impatrq/asmb/Docs/Certificado Prototipos 2.jpg

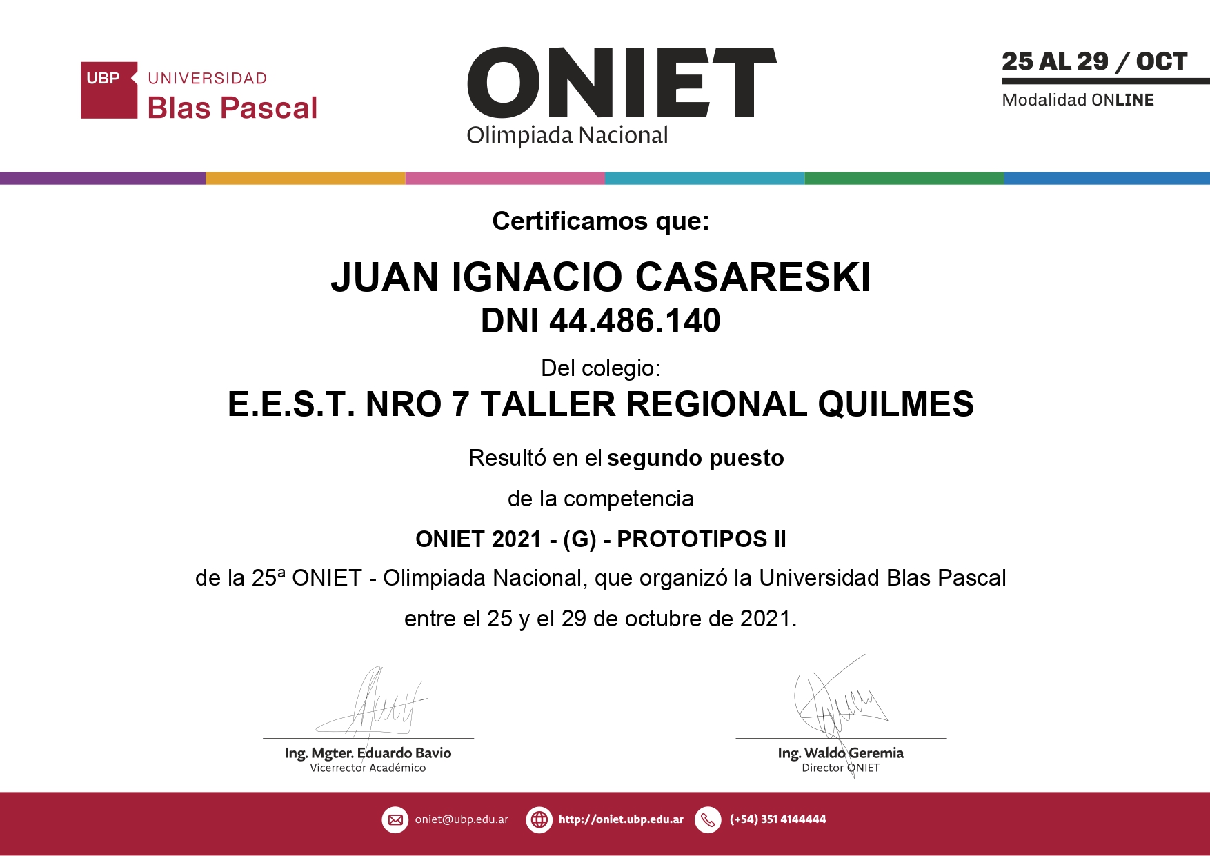
Docs/Certificado Prototipos 2.jpg
