impatrq/asmb/Docs/Imagenes/Adaptador de señal.png

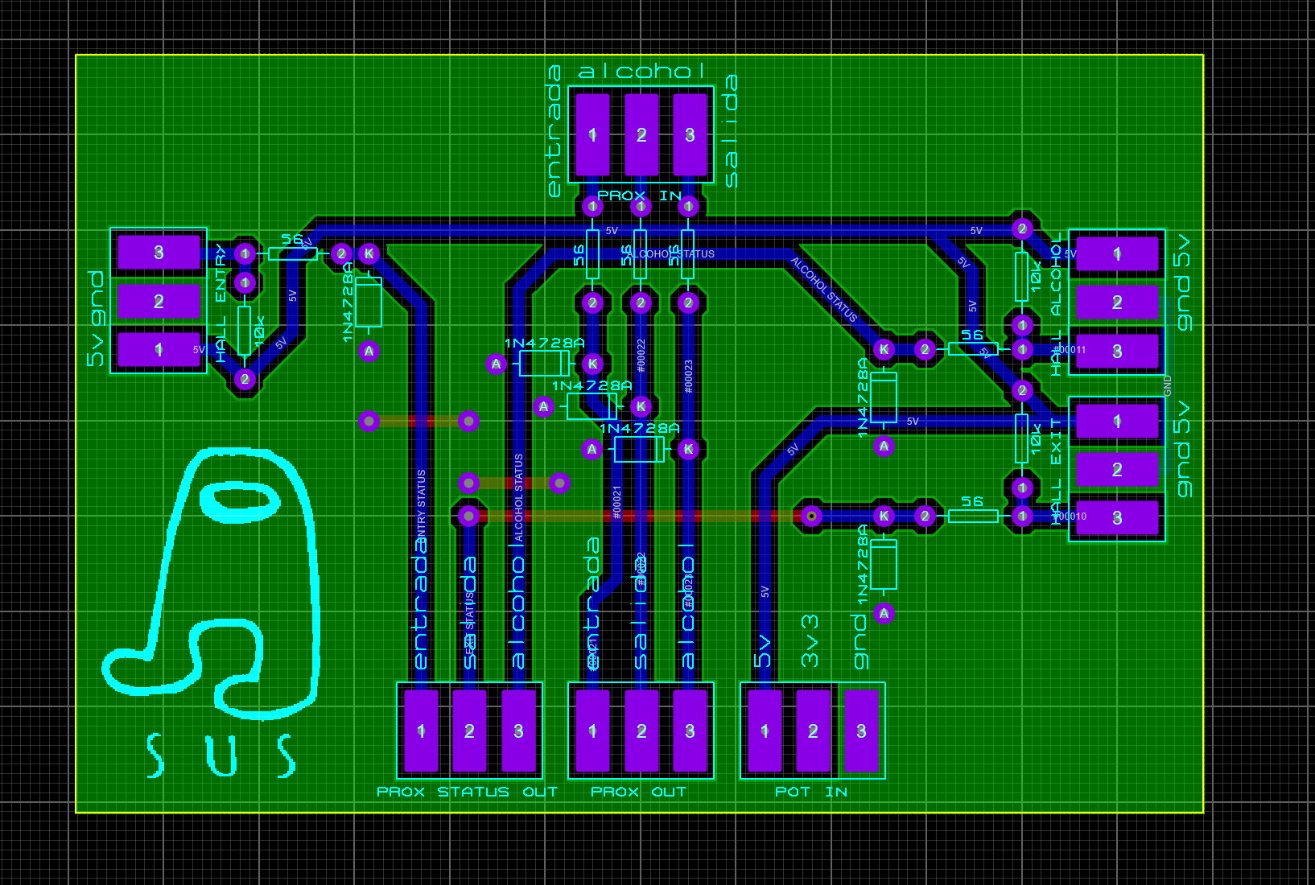
Docs/Imagenes/Adaptador de señal.png
