impatrq/asmb/Docs/Imagenes/Diagrama en Bloques.png

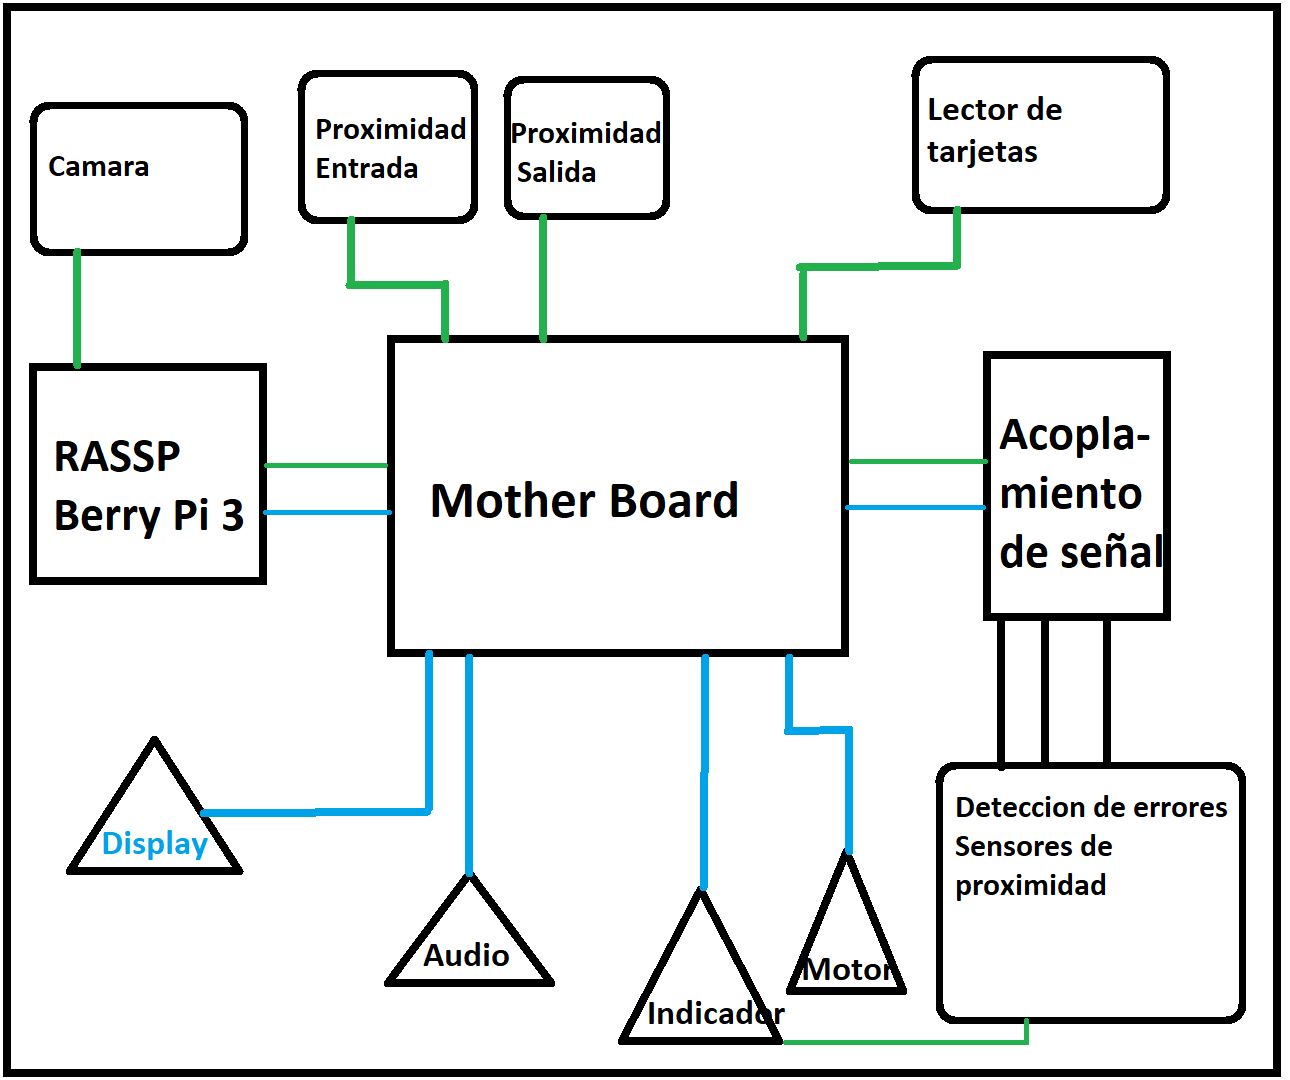
Docs/Imagenes/Diagrama en Bloques.png
