impatrq/asmb/Historias de Usuario/HU009 - Dispenser de alcohol/A1 - Croquis/Croquis.jpeg

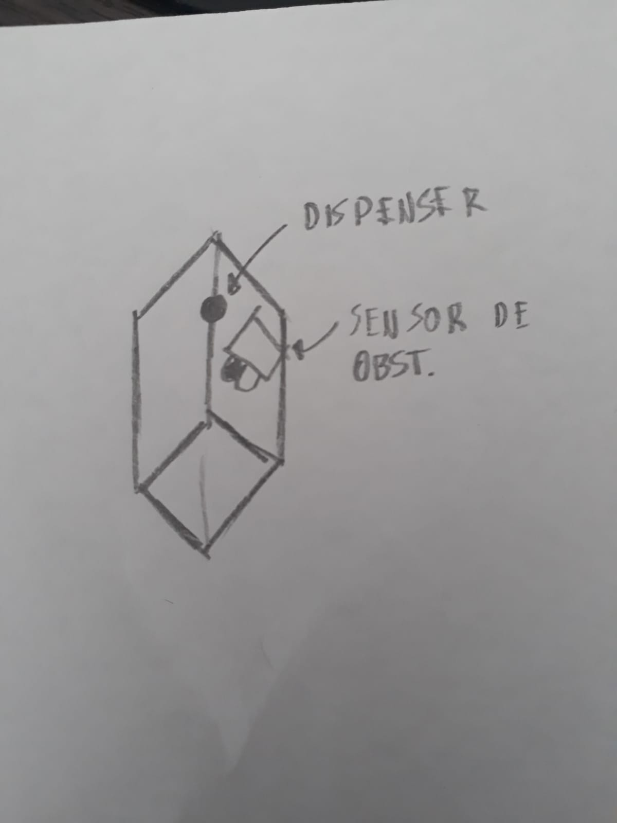
Historias de Usuario/HU009 - Dispenser de alcohol/A1 - Croquis/Croquis.jpeg
