impatrq/asmb/Historias de Usuario/HU009 - Dispenser de alcohol/A3 - Modelo 3d/Foto.png

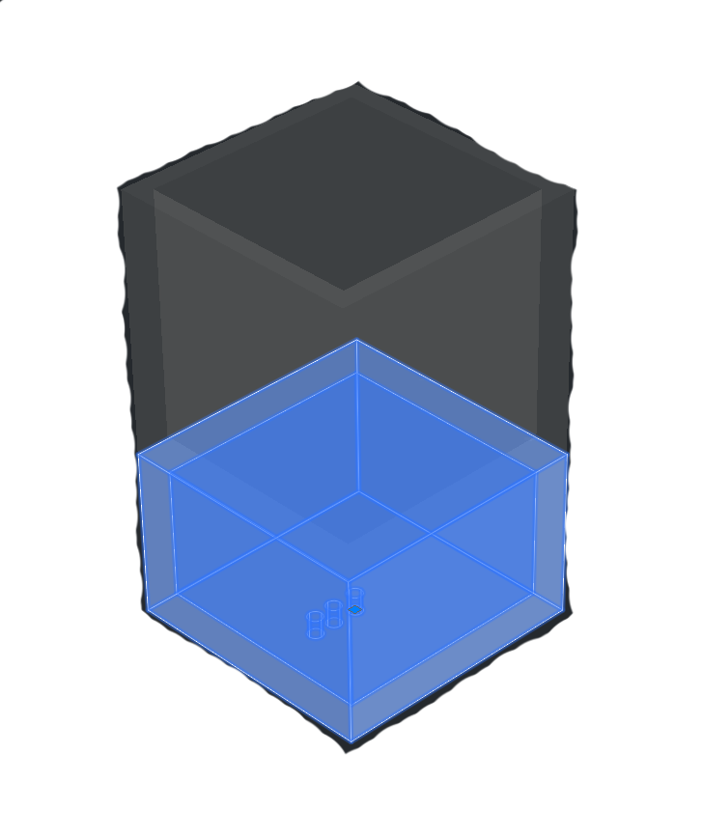
Historias de Usuario/HU009 - Dispenser de alcohol/A3 - Modelo 3d/Foto.png
