impatrq/asmb/Historias de Usuario/HU111 - Face recog/Resources/py_tutorials/py_ml/py_knn/py_knn_understanding/images/knn_theory.png

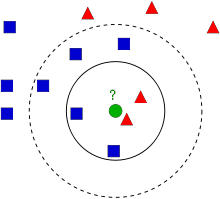
Historias de Usuario/HU111 - Face recog/Resources/py_tutorials/py_ml/py_knn/py_knn_understanding/images/knn_theory.png
