impatrq/asmb/Historias de Usuario/HU016 - Check In Empleados/A1 - Croquis/Croquis.jpeg

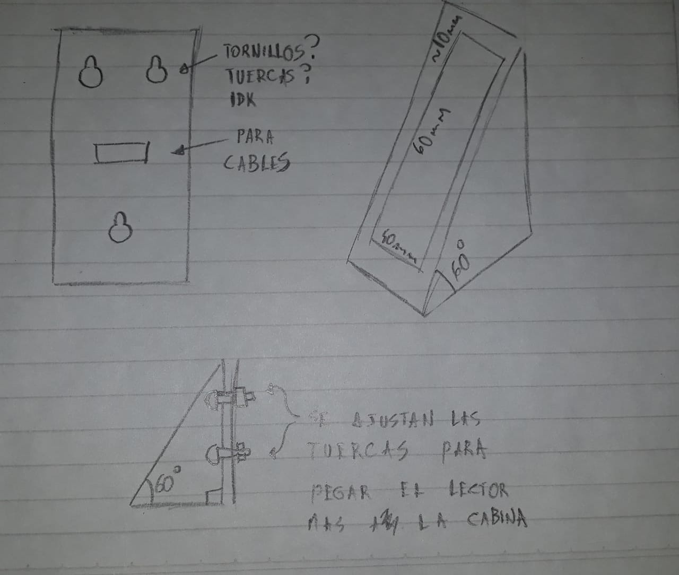
Historias de Usuario/HU016 - Check In Empleados/A1 - Croquis/Croquis.jpeg
