impatrq/asmb/Historias de Usuario/HU016 - Check In Empleados/A2 - Lugar en el croquis/Lugar en el croquis.png

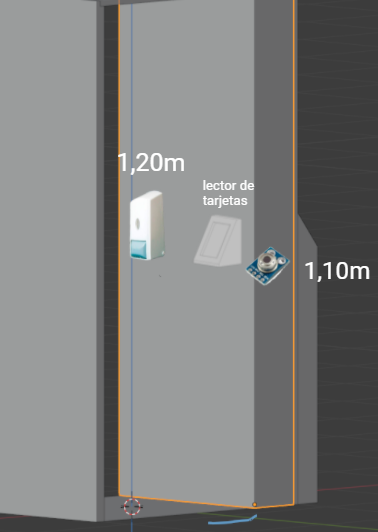
Historias de Usuario/HU016 - Check In Empleados/A2 - Lugar en el croquis/Lugar en el croquis.png
