impatrq/asmb/Historias de Usuario/HU016 - Check In Empleados/A3 - Modelo 3d/Foto del lector de tarjetas.png

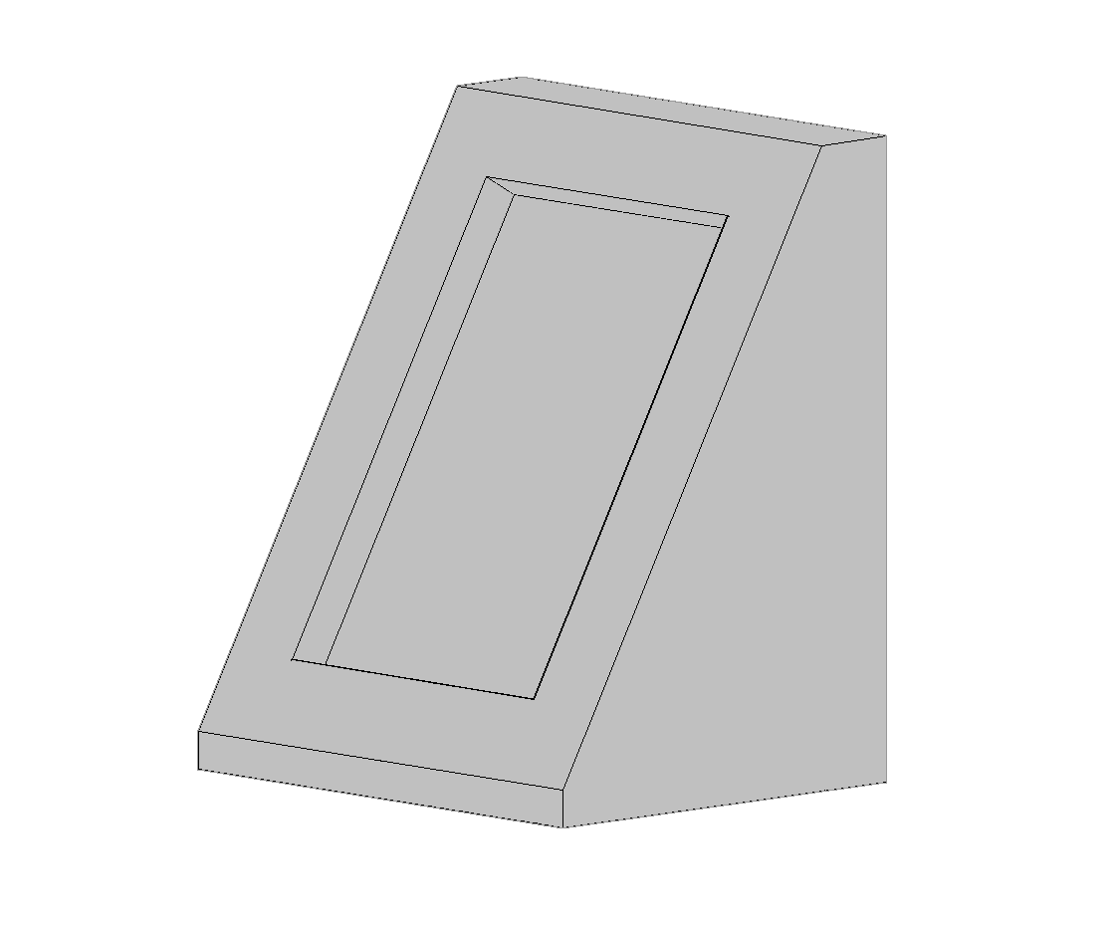
Historias de Usuario/HU016 - Check In Empleados/A3 - Modelo 3d/Foto del lector de tarjetas.png
