impatrq/asmb/Recursos/Circuitos/Dispenser de alcohol/Circuito dispenser.jpeg

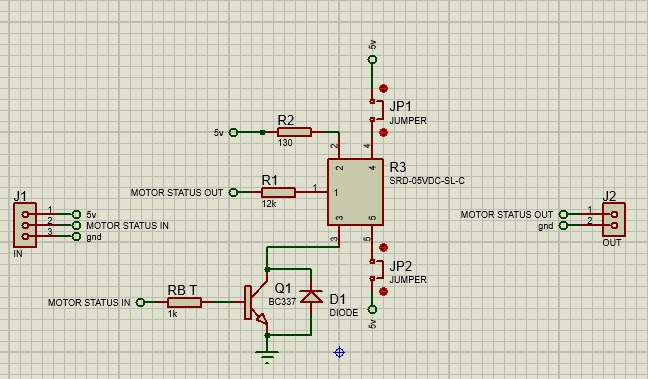
Recursos/Circuitos/Dispenser de alcohol/Circuito dispenser.jpeg
