impatrq/asmb/Recursos/Circuitos/Lector de tarjetas/Foto cirucito lector.jpeg

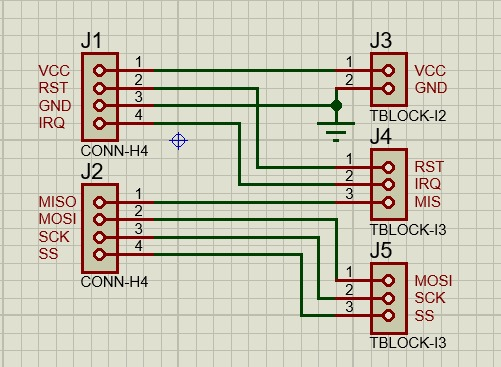
Recursos/Circuitos/Lector de tarjetas/Foto cirucito lector.jpeg
