impatrq/asmb/Recursos/Circuitos/Mother/Foto ciruito mother.jpeg

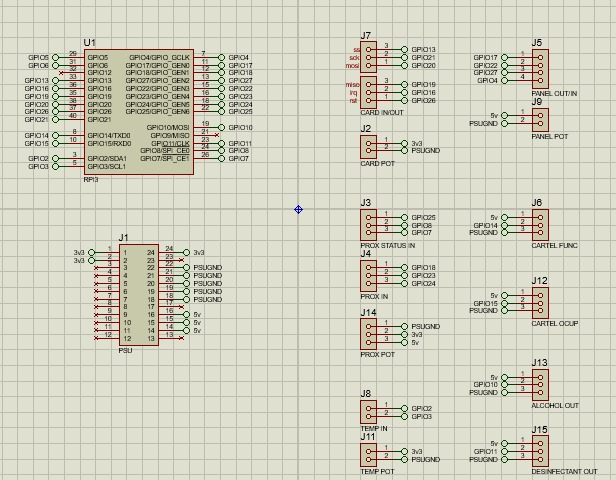
Recursos/Circuitos/Mother/Foto ciruito mother.jpeg
