impatrq/asmb/Recursos/Circuitos/Panel de estado/Foto circuito panel.jpeg

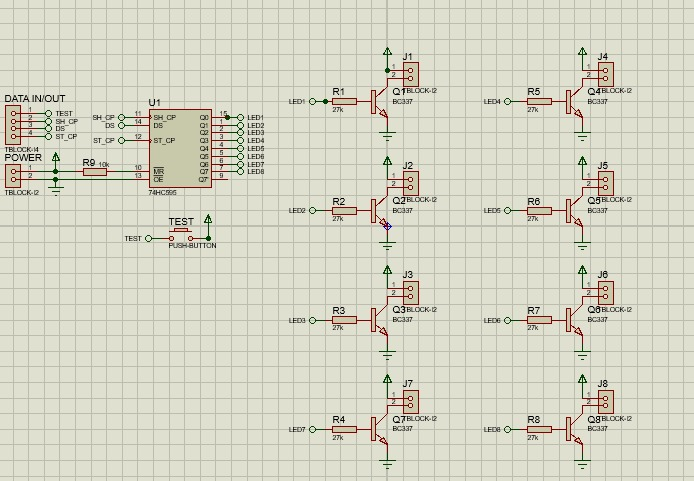
Recursos/Circuitos/Panel de estado/Foto circuito panel.jpeg
