impatrq/asmb/Recursos/Circuitos/Proximity sensors/Foto circuito Level.jpeg

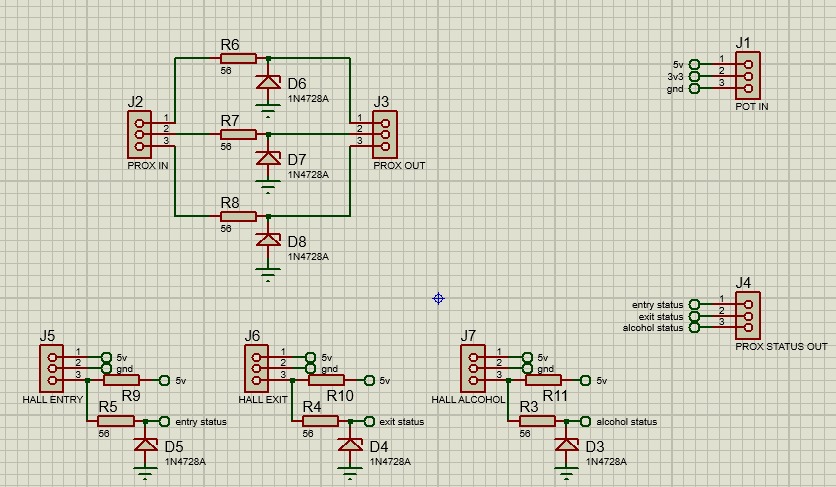
Recursos/Circuitos/Proximity sensors/Foto circuito Level.jpeg
