impatrq/asmb/Recursos/Modelos/Cabina general/Modelo Cabina General.jpeg

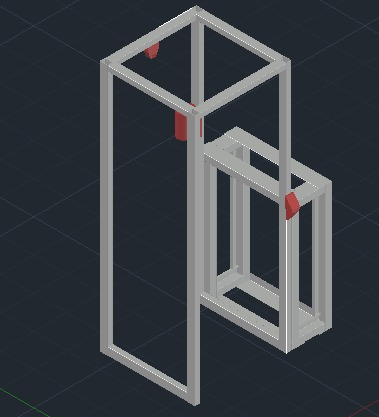
Recursos/Modelos/Cabina general/Modelo Cabina General.jpeg
