impatrq/asmb/Recursos/Modelos/Cartel ocupado/Cartel Ocupado.jpeg

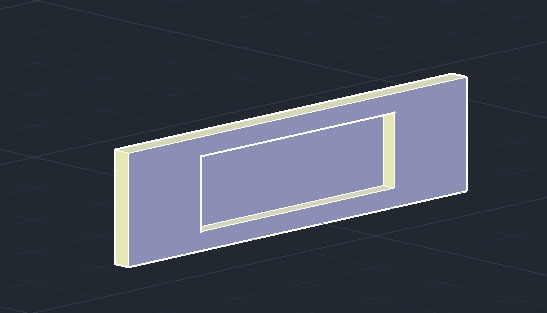
Recursos/Modelos/Cartel ocupado/Cartel Ocupado.jpeg
