impatrq/asmb/Recursos/Modelos/Dispenser de alcohol en gel/Dispenser.jpeg

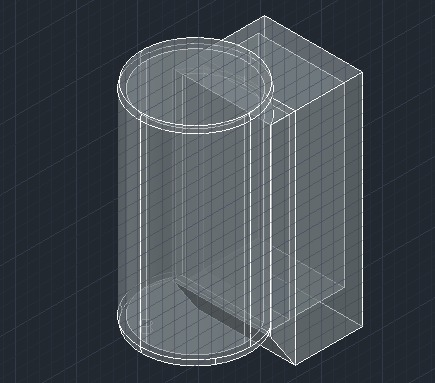
Recursos/Modelos/Dispenser de alcohol en gel/Dispenser.jpeg
