impatrq/asmb/Recursos/Modelos/Lector de tarjetas/Lector.jpeg

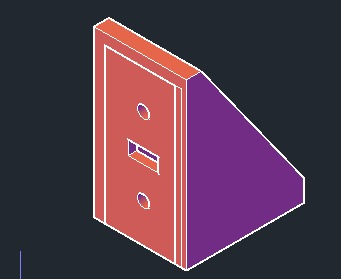
Recursos/Modelos/Lector de tarjetas/Lector.jpeg
