impatrq/asmb/Recursos/Modelos/Sensor de temperatura/Sensor de temp..jpeg

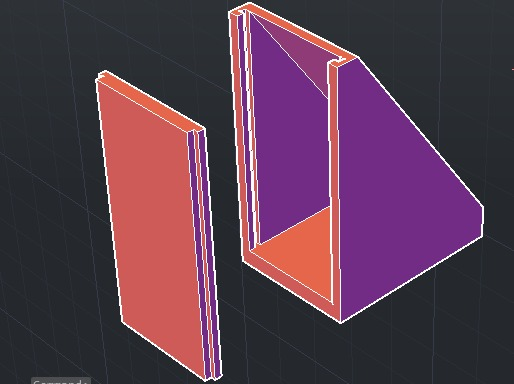
Recursos/Modelos/Sensor de temperatura/Sensor de temp..jpeg
