impatrq/asmb/Recursos/Video Presentación/Fotos/26c4ca4a28fdd9ee4a0b5ad8b2b49a2f3947dffb_full.jpg

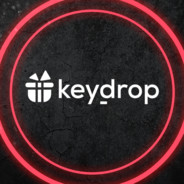
Recursos/Video Presentación/Fotos/26c4ca4a28fdd9ee4a0b5ad8b2b49a2f3947dffb_full.jpg
