impatrq/asmb/Recursos/Video Presentación/Fotos/CASI XD.jpg

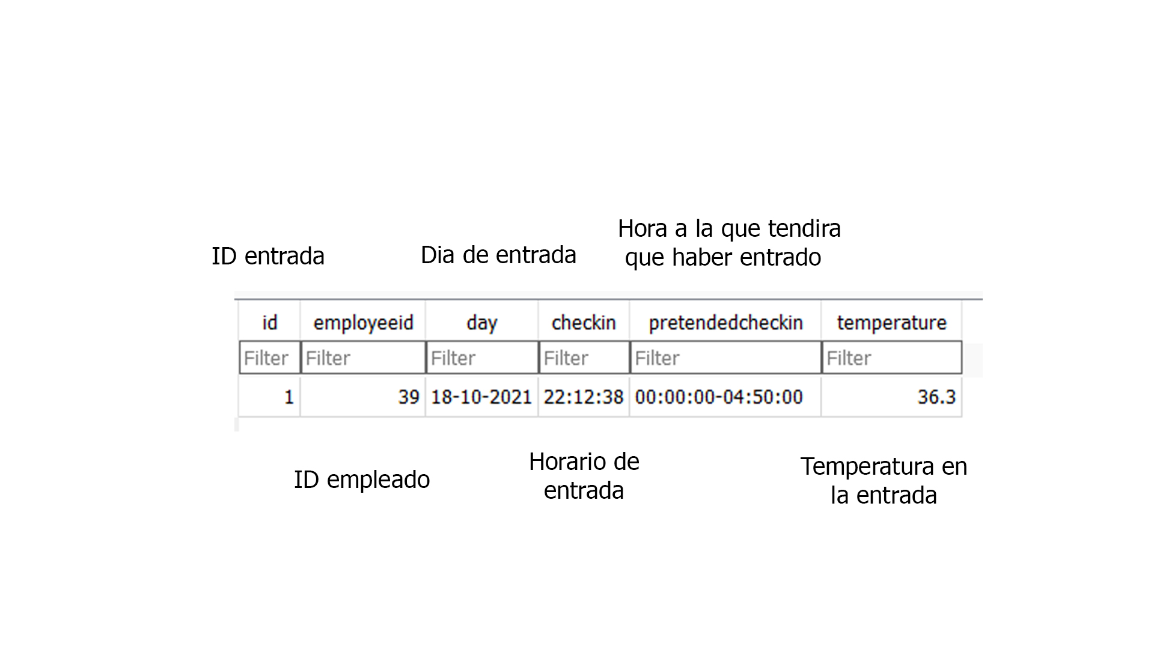
Recursos/Video Presentación/Fotos/CASI XD.jpg
