impatrq/asmb/Recursos/Video Presentación/Fotos/entrada_aeropuerto_2.jpg

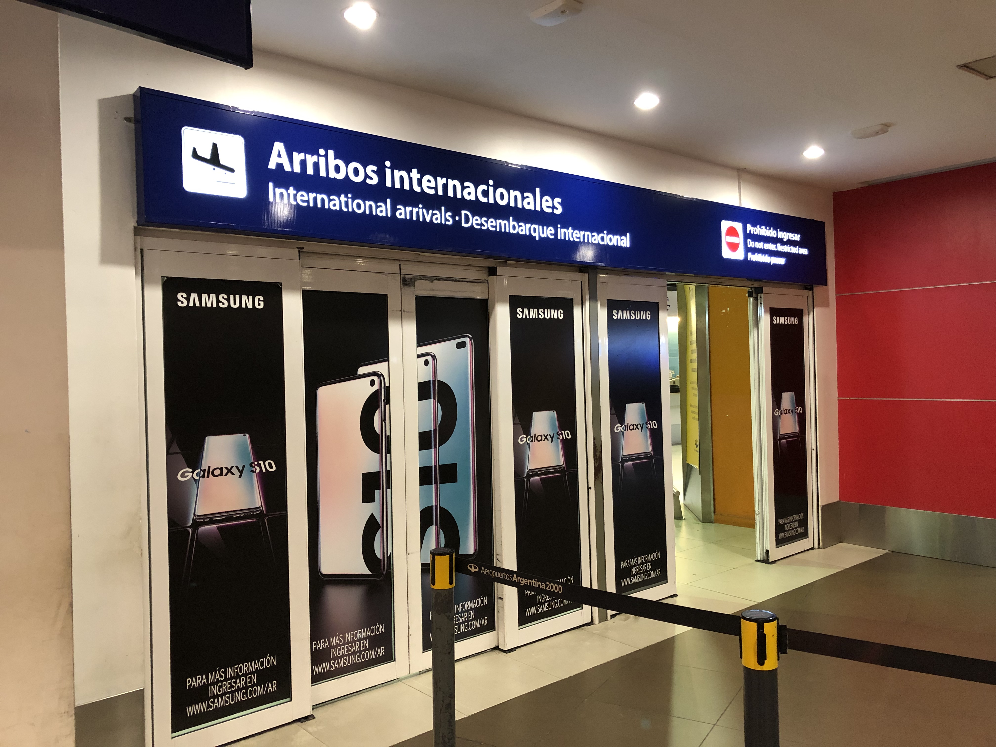
Recursos/Video Presentación/Fotos/entrada_aeropuerto_2.jpg
