impatrq/asmb/Recursos/Video Presentación/Fotos/entrada_comercio_4.jpg

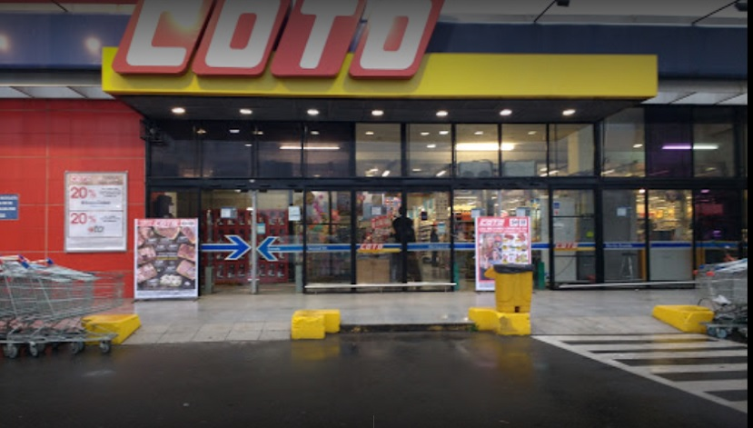
Recursos/Video Presentación/Fotos/entrada_comercio_4.jpg
