impatrq/asmb/Recursos/Video Presentación/Fotos/entrada_escuela_3.jpg

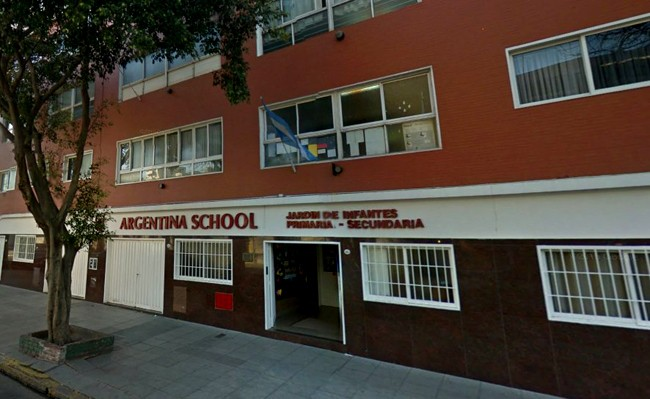
Recursos/Video Presentación/Fotos/entrada_escuela_3.jpg
