impatrq/asmb/Recursos/Video Presentación/Fotos/hospital_frente_1 (1).jpg

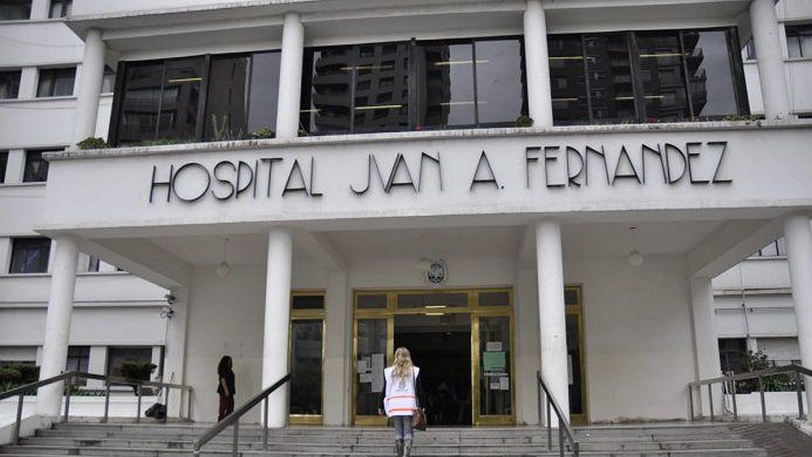
Recursos/Video Presentación/Fotos/hospital_frente_1 (1).jpg
