impatrq/asmb/Recursos/Video Presentación/Fotos/Muestras de proyectos.jpg

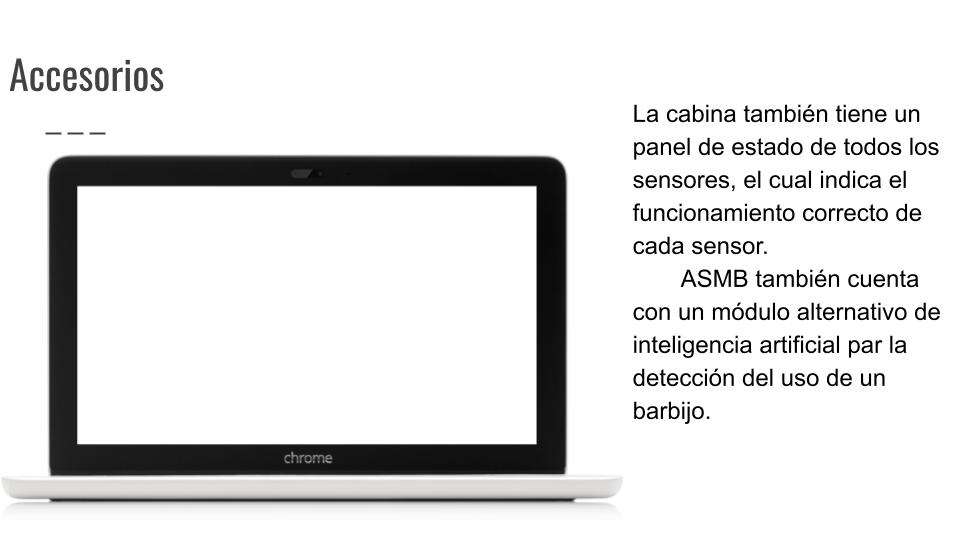
Recursos/Video Presentación/Fotos/Muestras de proyectos.jpg
