impatrq/asmb/Recursos/Video Presentación/Fotos/Muestras_de_proyectos.jpg

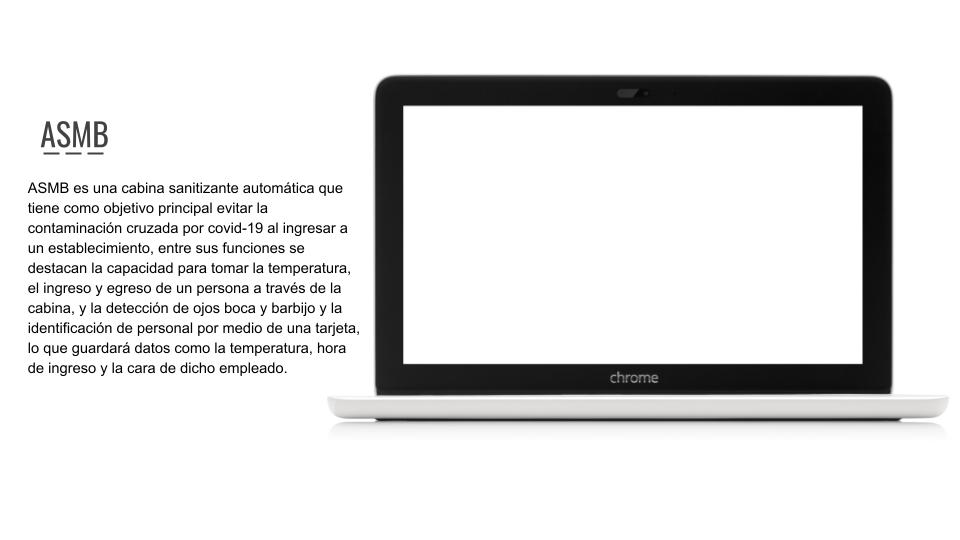
Recursos/Video Presentación/Fotos/Muestras_de_proyectos.jpg
