impatrq/asmb/Recursos/Video Presentación/Fotos/Muestras_de_proyectos_1.jpg

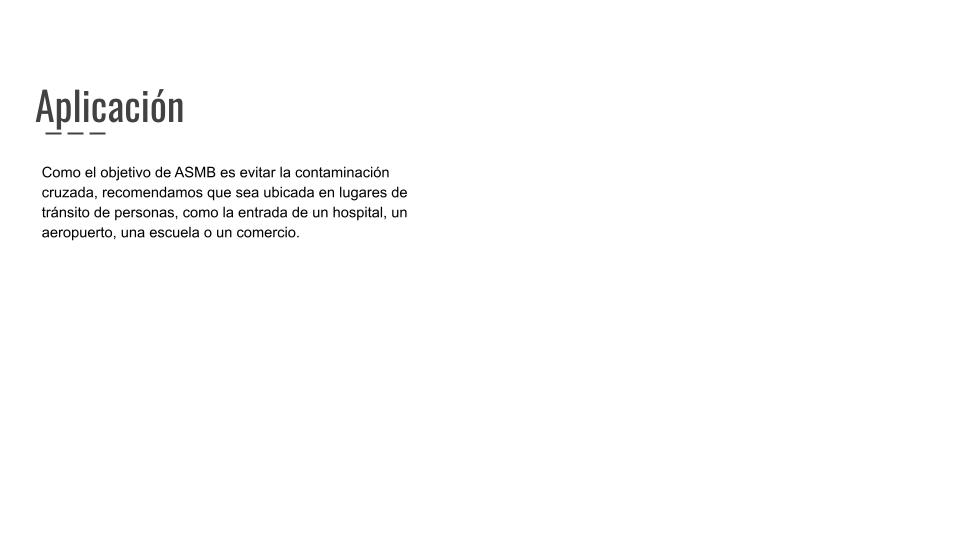
Recursos/Video Presentación/Fotos/Muestras_de_proyectos_1.jpg
