impatrq/asmb/Recursos/Video Presentación/Fotos/Muestras_de_proyectos_2.jpg

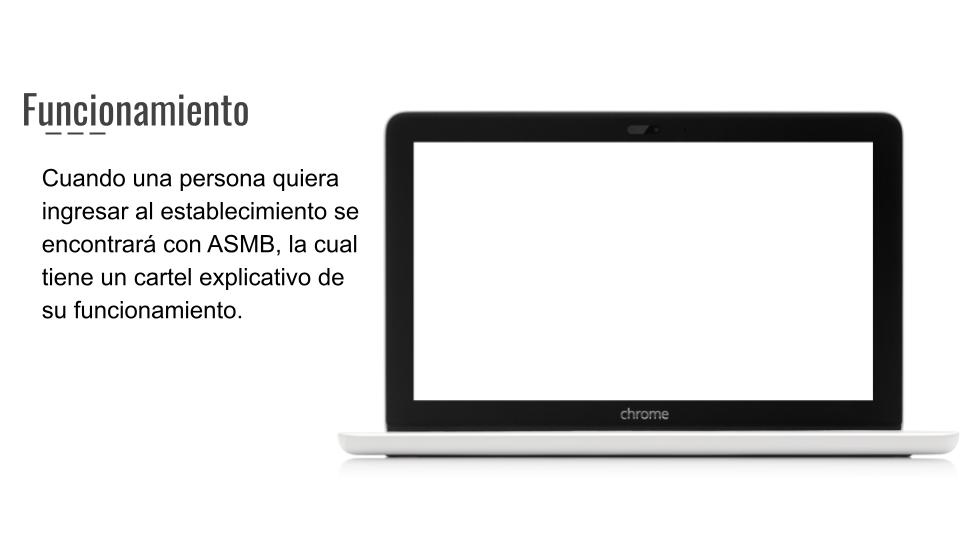
Recursos/Video Presentación/Fotos/Muestras_de_proyectos_2.jpg
