impatrq/asmb/Recursos/Video Presentación/Fotos/Muestras_de_proyectos_5 (1).jpg

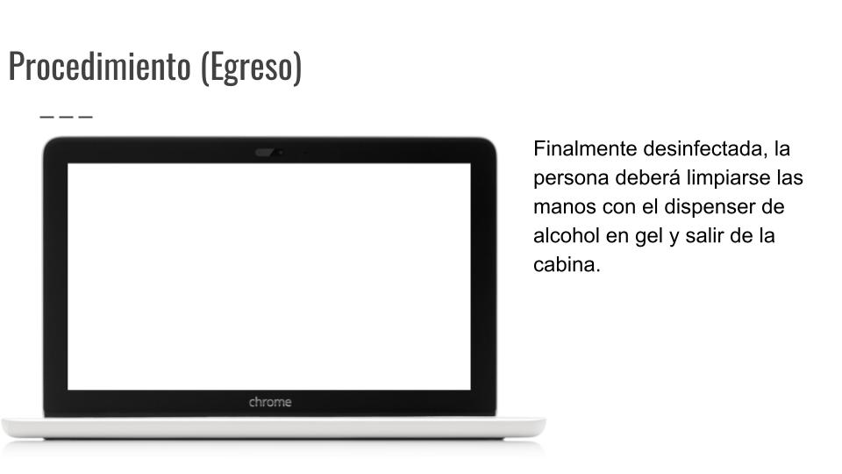
Recursos/Video Presentación/Fotos/Muestras_de_proyectos_5 (1).jpg
