impatrq/asmb/Recursos/Video Presentación/Fotos/Muestras_de_proyectos_6 (1).jpg

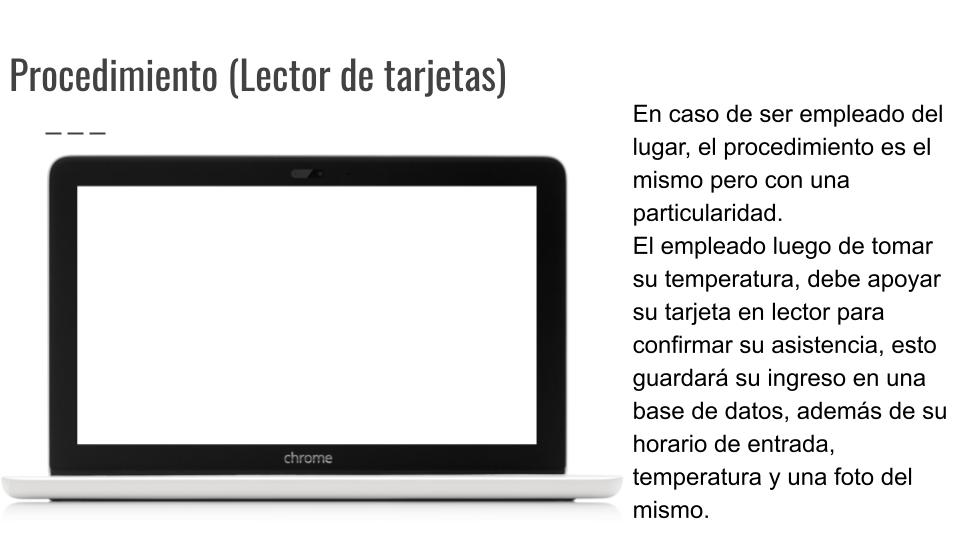
Recursos/Video Presentación/Fotos/Muestras_de_proyectos_6 (1).jpg
