impatrq/asmb/Recursos/Video Presentación/Fotos/Muestras_de_proyectos_7.jpg

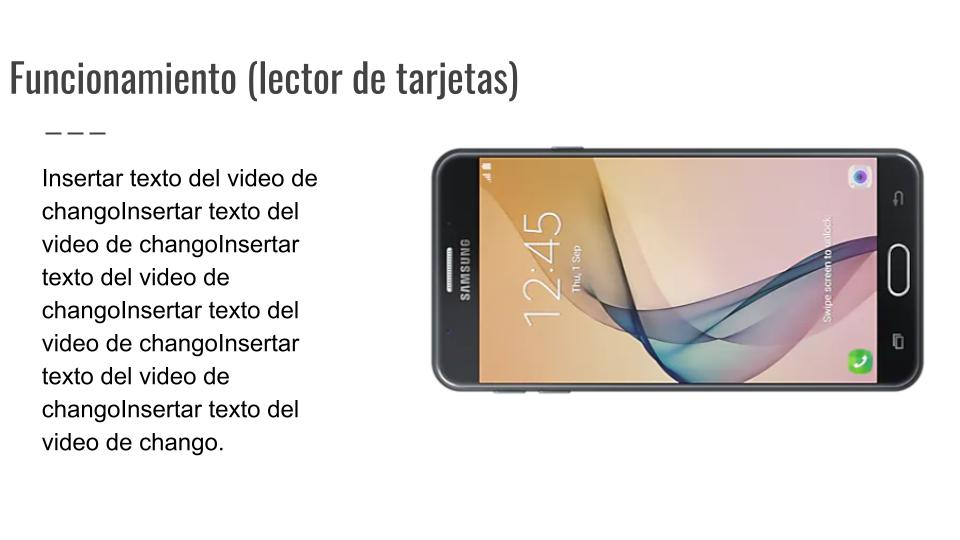
Recursos/Video Presentación/Fotos/Muestras_de_proyectos_7.jpg
