impatrq/asmb/Docs/Construccion de la cabina/Fotos/FotoEstructura.jpg

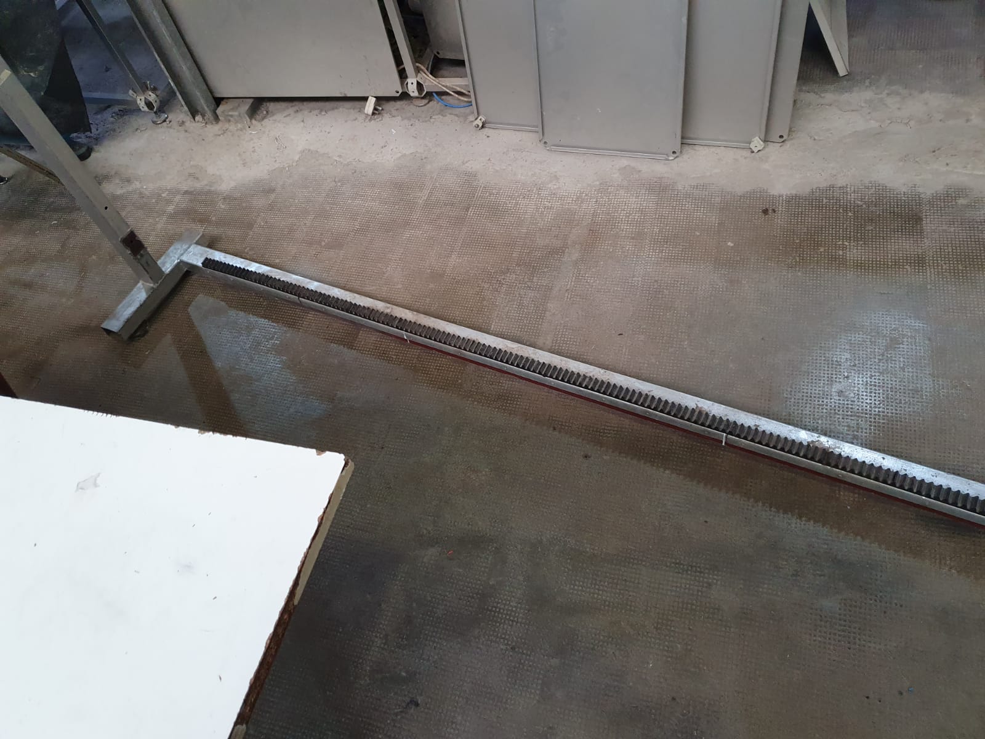
Docs/Construccion de la cabina/Fotos/FotoEstructura.jpg
