impatrq/asmb/Historias de Usuario/HU111 - Face recog/Resources/py_tutorials/py_calib3d/py_depthmap/images/disparity_map.jpg

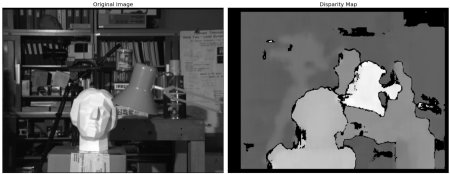
Historias de Usuario/HU111 - Face recog/Resources/py_tutorials/py_calib3d/py_depthmap/images/disparity_map.jpg
