impatrq/asmb/Historias de Usuario/HU111 - Face recog/Resources/py_tutorials/py_calib3d/py_depthmap/images/stereo_depth.jpg

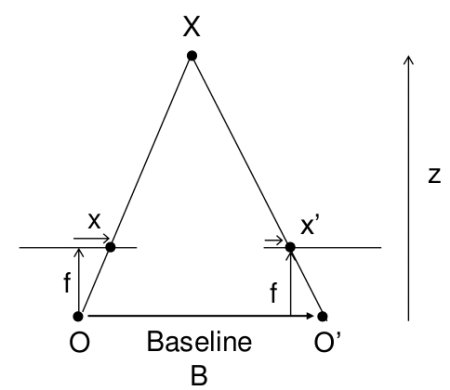
Historias de Usuario/HU111 - Face recog/Resources/py_tutorials/py_calib3d/py_depthmap/images/stereo_depth.jpg
