impatrq/asmb/Historias de Usuario/HU111 - Face recog/Resources/py_tutorials/py_calib3d/py_epipolar_geometry/images/essential_matrix.jpg

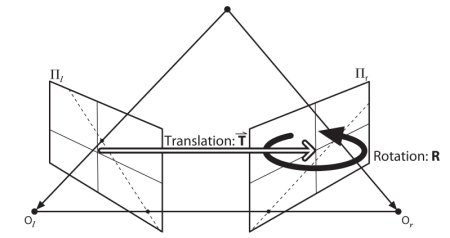
Historias de Usuario/HU111 - Face recog/Resources/py_tutorials/py_calib3d/py_epipolar_geometry/images/essential_matrix.jpg
