impatrq/asmb/Historias de Usuario/HU111 - Face recog/Resources/py_tutorials/py_core/py_basic_ops/images/roi.jpg

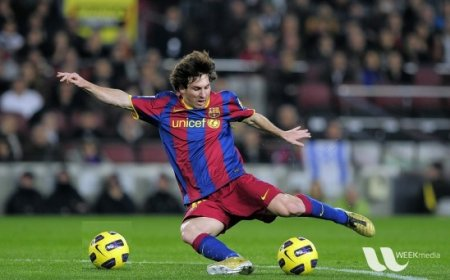
Historias de Usuario/HU111 - Face recog/Resources/py_tutorials/py_core/py_basic_ops/images/roi.jpg
