impatrq/asmb/Historias de Usuario/HU111 - Face recog/Resources/py_tutorials/py_core/py_image_arithmetics/images/overlay.jpg

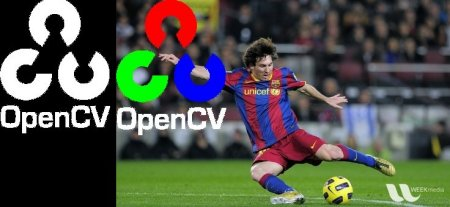
Historias de Usuario/HU111 - Face recog/Resources/py_tutorials/py_core/py_image_arithmetics/images/overlay.jpg
