impatrq/asmb/Historias de Usuario/HU111 - Face recog/Resources/py_tutorials/py_feature2d/images/matching.jpg

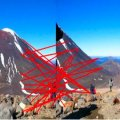
Historias de Usuario/HU111 - Face recog/Resources/py_tutorials/py_feature2d/images/matching.jpg
