impatrq/asmb/Historias de Usuario/HU111 - Face recog/Resources/py_tutorials/py_feature2d/py_fast/images/fast_kp.jpg

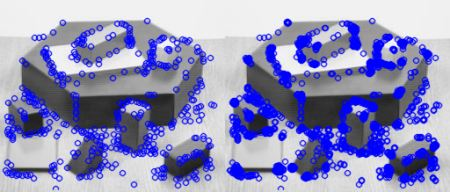
Historias de Usuario/HU111 - Face recog/Resources/py_tutorials/py_feature2d/py_fast/images/fast_kp.jpg
