impatrq/asmb/Historias de Usuario/HU111 - Face recog/Resources/py_tutorials/py_feature2d/py_feature_homography/images/homography_findobj.jpg

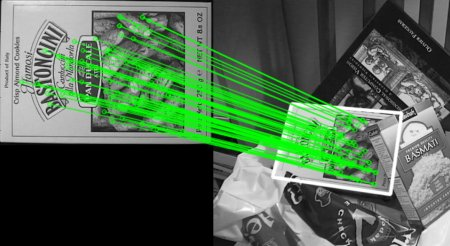
Historias de Usuario/HU111 - Face recog/Resources/py_tutorials/py_feature2d/py_feature_homography/images/homography_findobj.jpg
