impatrq/asmb/Historias de Usuario/HU111 - Face recog/Resources/py_tutorials/py_feature2d/py_features_harris/images/harris_region.jpg

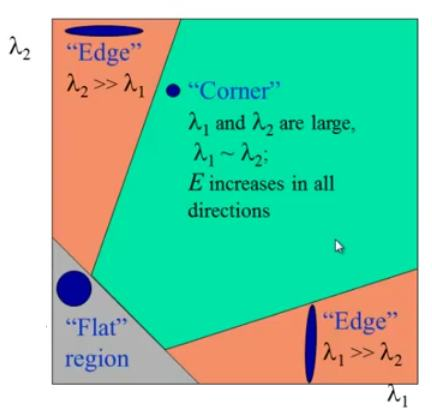
Historias de Usuario/HU111 - Face recog/Resources/py_tutorials/py_feature2d/py_features_harris/images/harris_region.jpg
