impatrq/asmb/Historias de Usuario/HU111 - Face recog/Resources/py_tutorials/py_feature2d/py_features_harris/images/subpixel3.png

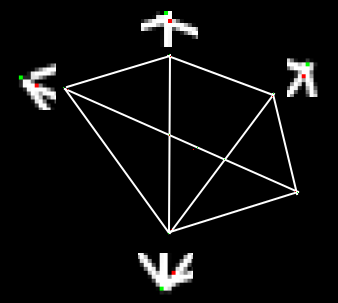
Historias de Usuario/HU111 - Face recog/Resources/py_tutorials/py_feature2d/py_features_harris/images/subpixel3.png
