impatrq/asmb/Historias de Usuario/HU111 - Face recog/Resources/py_tutorials/py_feature2d/py_features_meaning/images/feature_simple.png

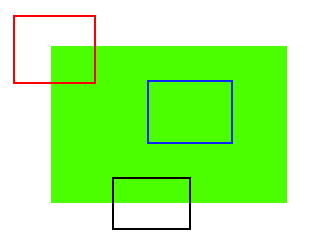
Historias de Usuario/HU111 - Face recog/Resources/py_tutorials/py_feature2d/py_features_meaning/images/feature_simple.png
