impatrq/asmb/Historias de Usuario/HU111 - Face recog/Resources/py_tutorials/py_feature2d/py_shi_tomasi/images/shitomasi_space.png

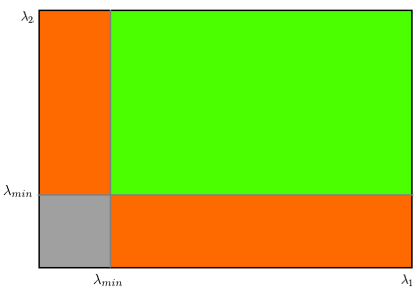
Historias de Usuario/HU111 - Face recog/Resources/py_tutorials/py_feature2d/py_shi_tomasi/images/shitomasi_space.png
