impatrq/asmb/Historias de Usuario/HU111 - Face recog/Resources/py_tutorials/py_gui/py_trackbar/images/trackbar_screenshot.jpg

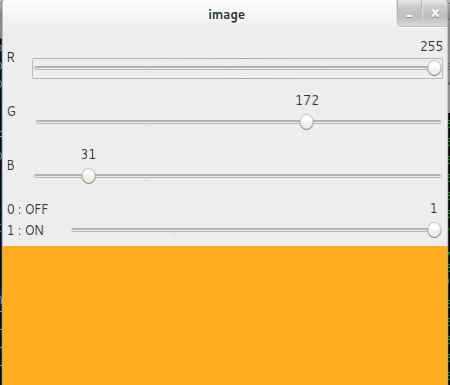
Historias de Usuario/HU111 - Face recog/Resources/py_tutorials/py_gui/py_trackbar/images/trackbar_screenshot.jpg
