impatrq/asmb/Historias de Usuario/HU111 - Face recog/Resources/py_tutorials/py_imgproc/images/blurring.jpg

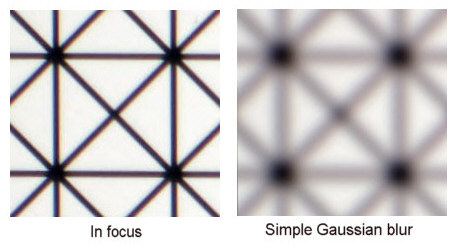
Historias de Usuario/HU111 - Face recog/Resources/py_tutorials/py_imgproc/images/blurring.jpg
