impatrq/asmb/Historias de Usuario/HU111 - Face recog/Resources/py_tutorials/py_imgproc/py_canny/images/nms.jpg

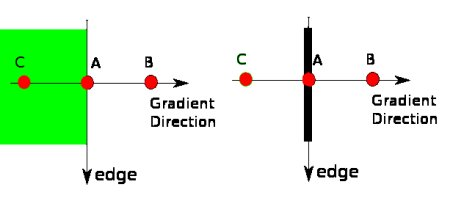
Historias de Usuario/HU111 - Face recog/Resources/py_tutorials/py_imgproc/py_canny/images/nms.jpg
