impatrq/asmb/Historias de Usuario/HU111 - Face recog/Resources/py_tutorials/py_imgproc/py_colorspaces/images/frame.jpg

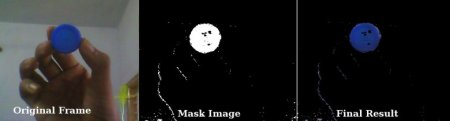
Historias de Usuario/HU111 - Face recog/Resources/py_tutorials/py_imgproc/py_colorspaces/images/frame.jpg
