impatrq/asmb/Historias de Usuario/HU111 - Face recog/Resources/py_tutorials/py_imgproc/py_contours/images/contour_hierarchy.jpg

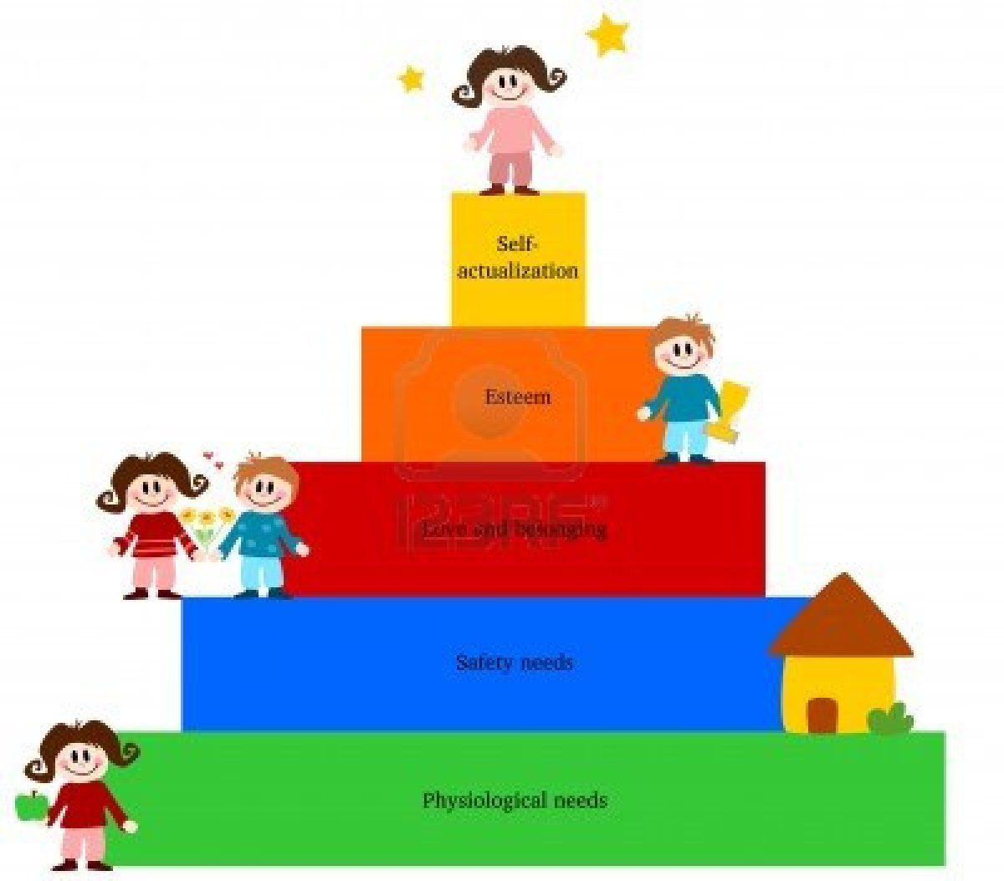
Historias de Usuario/HU111 - Face recog/Resources/py_tutorials/py_imgproc/py_contours/images/contour_hierarchy.jpg
