impatrq/asmb/Historias de Usuario/HU111 - Face recog/Resources/py_tutorials/py_imgproc/py_contours/py_contour_features/images/circumcircle.png

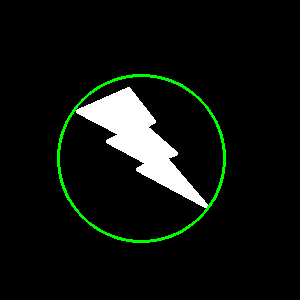
Historias de Usuario/HU111 - Face recog/Resources/py_tutorials/py_imgproc/py_contours/py_contour_features/images/circumcircle.png
