impatrq/asmb/Historias de Usuario/HU111 - Face recog/Resources/py_tutorials/py_imgproc/py_contours/py_contour_features/images/convexitydefects.jpg

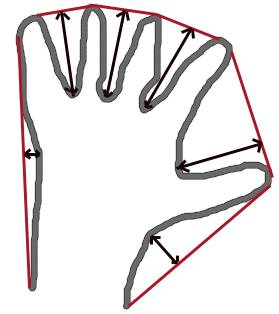
Historias de Usuario/HU111 - Face recog/Resources/py_tutorials/py_imgproc/py_contours/py_contour_features/images/convexitydefects.jpg
