impatrq/asmb/Historias de Usuario/HU111 - Face recog/Resources/py_tutorials/py_imgproc/py_contours/py_contours_hierarchy/images/ccomp_hierarchy.png

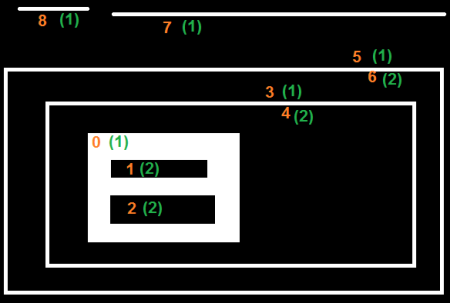
Historias de Usuario/HU111 - Face recog/Resources/py_tutorials/py_imgproc/py_contours/py_contours_hierarchy/images/ccomp_hierarchy.png
