impatrq/asmb/Historias de Usuario/HU111 - Face recog/Resources/py_tutorials/py_imgproc/py_histograms/py_2d_histogram/images/2dhist_opencv.jpg

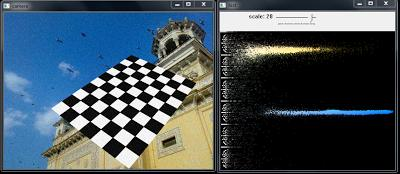
Historias de Usuario/HU111 - Face recog/Resources/py_tutorials/py_imgproc/py_histograms/py_2d_histogram/images/2dhist_opencv.jpg
