impatrq/asmb/Historias de Usuario/HU111 - Face recog/Resources/py_tutorials/py_imgproc/py_histograms/py_histogram_backprojection/images/backproject_opencv.jpg

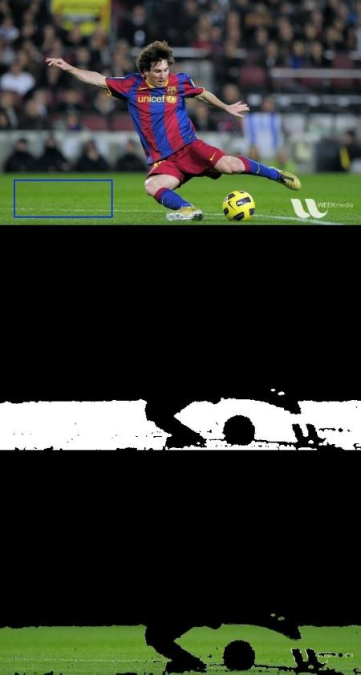
Historias de Usuario/HU111 - Face recog/Resources/py_tutorials/py_imgproc/py_histograms/py_histogram_backprojection/images/backproject_opencv.jpg
