impatrq/asmb/Historias de Usuario/HU111 - Face recog/Resources/py_tutorials/py_imgproc/py_histograms/py_histogram_begins/images/histogram_matplotlib.jpg

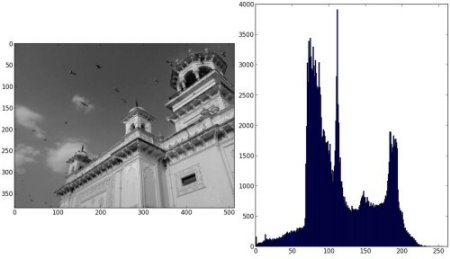
Historias de Usuario/HU111 - Face recog/Resources/py_tutorials/py_imgproc/py_histograms/py_histogram_begins/images/histogram_matplotlib.jpg
