impatrq/asmb/Historias de Usuario/HU111 - Face recog/Resources/py_tutorials/py_imgproc/py_houghlines/images/houghlinesdemo.gif

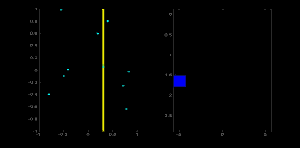
Historias de Usuario/HU111 - Face recog/Resources/py_tutorials/py_imgproc/py_houghlines/images/houghlinesdemo.gif
