impatrq/asmb/Historias de Usuario/HU111 - Face recog/Resources/py_tutorials/py_imgproc/py_morphological_ops/images/closing.png

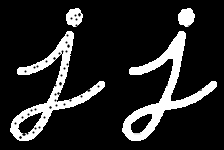
Historias de Usuario/HU111 - Face recog/Resources/py_tutorials/py_imgproc/py_morphological_ops/images/closing.png
