impatrq/asmb/Historias de Usuario/HU111 - Face recog/Resources/py_tutorials/py_imgproc/py_transforms/py_fourier_transform/images/fft5.jpg

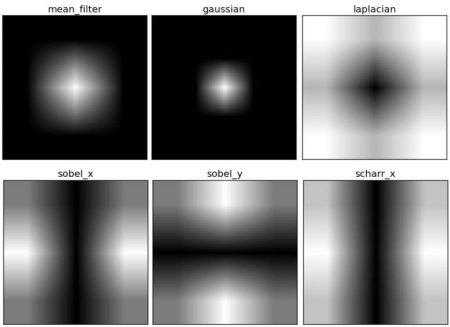
Historias de Usuario/HU111 - Face recog/Resources/py_tutorials/py_imgproc/py_transforms/py_fourier_transform/images/fft5.jpg
