impatrq/asmb/Historias de Usuario/HU111 - Face recog/Resources/py_tutorials/py_ml/py_kmeans/py_kmeans_opencv/images/oc_2d_clustered.jpg

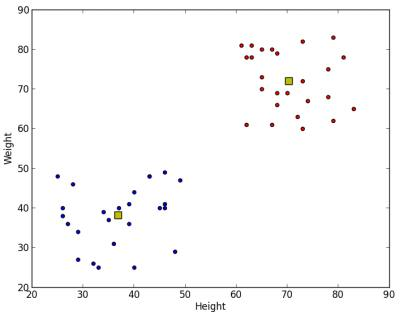
Historias de Usuario/HU111 - Face recog/Resources/py_tutorials/py_ml/py_kmeans/py_kmeans_opencv/images/oc_2d_clustered.jpg
