impatrq/asmb/Historias de Usuario/HU111 - Face recog/Resources/py_tutorials/py_ml/py_kmeans/py_kmeans_understanding/images/final_clusters.jpg

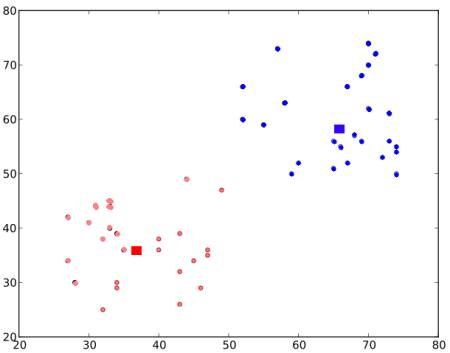
Historias de Usuario/HU111 - Face recog/Resources/py_tutorials/py_ml/py_kmeans/py_kmeans_understanding/images/final_clusters.jpg
