impatrq/asmb/Historias de Usuario/HU111 - Face recog/Resources/py_tutorials/py_ml/py_svm/py_svm_basics/images/svm_basics1.png

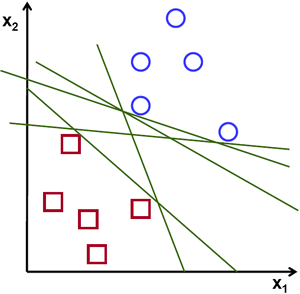
Historias de Usuario/HU111 - Face recog/Resources/py_tutorials/py_ml/py_svm/py_svm_basics/images/svm_basics1.png
