impatrq/asmb/Historias de Usuario/HU111 - Face recog/Resources/py_tutorials/py_ml/py_svm/py_svm_opencv/images/deskew.jpg

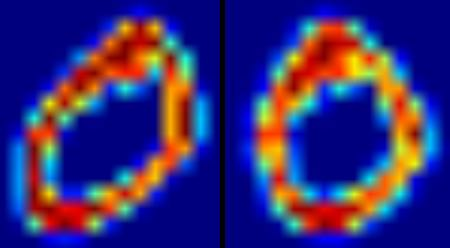
Historias de Usuario/HU111 - Face recog/Resources/py_tutorials/py_ml/py_svm/py_svm_opencv/images/deskew.jpg
