impatrq/asmb/Historias de Usuario/HU111 - Face recog/Resources/py_tutorials/py_photo/py_hdr/images/exposures.jpg

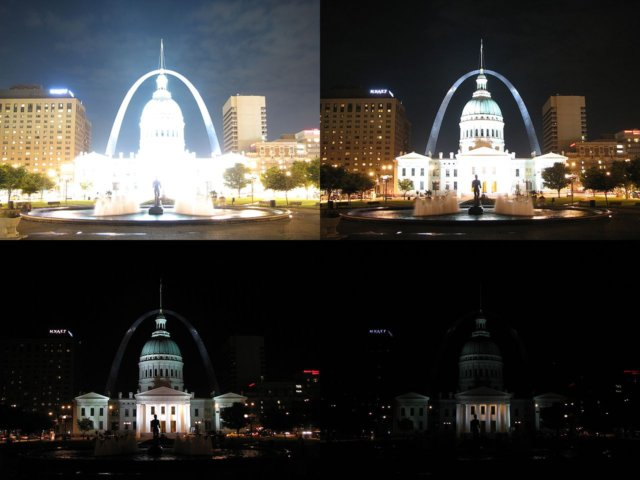
Historias de Usuario/HU111 - Face recog/Resources/py_tutorials/py_photo/py_hdr/images/exposures.jpg
