impatrq/asmb/Historias de Usuario/HU111 - Face recog/Resources/py_tutorials/py_photo/py_hdr/images/fusion_mertens.jpg

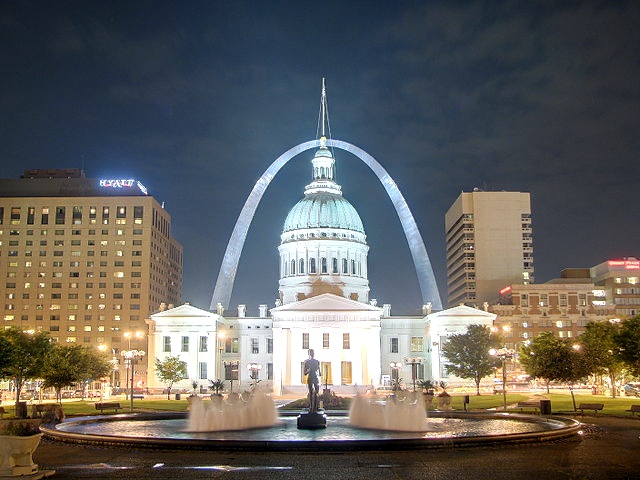
Historias de Usuario/HU111 - Face recog/Resources/py_tutorials/py_photo/py_hdr/images/fusion_mertens.jpg
