impatrq/asmb/Historias de Usuario/HU111 - Face recog/Resources/py_tutorials/py_photo/py_inpainting/images/inpaint_basics.jpg

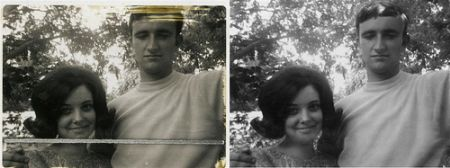
Historias de Usuario/HU111 - Face recog/Resources/py_tutorials/py_photo/py_inpainting/images/inpaint_basics.jpg
