impatrq/asmb/Historias de Usuario/HU111 - Face recog/Resources/py_tutorials/py_setup/py_setup_in_windows/images/Capture5.png

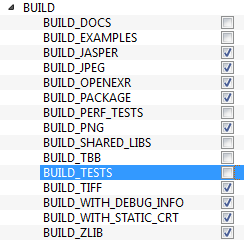
Historias de Usuario/HU111 - Face recog/Resources/py_tutorials/py_setup/py_setup_in_windows/images/Capture5.png
