impatrq/asmb/Historias de Usuario/HU111 - Face recog/Resources/py_tutorials/py_gui/py_drawing_functions/images/drawing_result.jpg

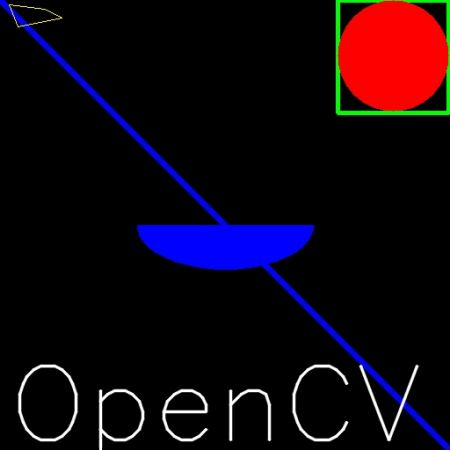
Historias de Usuario/HU111 - Face recog/Resources/py_tutorials/py_gui/py_drawing_functions/images/drawing_result.jpg
