impatrq/asmb/Historias de Usuario/HU111 - Face recog/Resources/py_tutorials/py_photo/py_non_local_means/images/nlm_result1.jpg

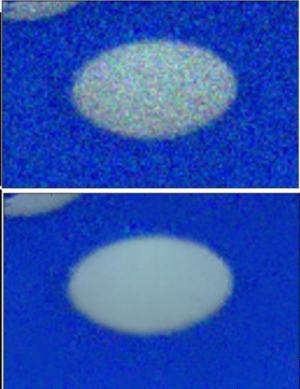
Historias de Usuario/HU111 - Face recog/Resources/py_tutorials/py_photo/py_non_local_means/images/nlm_result1.jpg
