impatrq/asmb/Historias de Usuario/Tareas extras/Crear clase general/Tests.py

class hola:
    def __init__(self, ) -> None:
        self.a = 'a'
        print(self.a)

    class chau:
        def uwu(a):
            print(a)

asd =  hola()
asdd = hola.chau
asdd.uwu(13123)
asdd.uwu(13123)
